Nesstle05/Ebook-Reader/Images/poza2_pcb.jpg

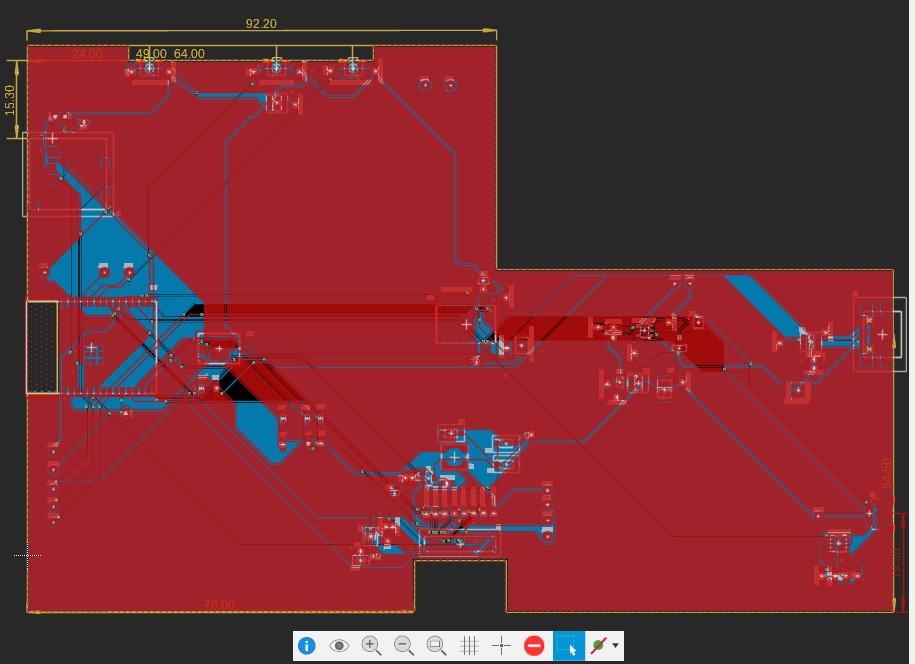
Images/poza2_pcb.jpg
